rodan/proto430/firmware/i2c_read/list_helper.h

#ifndef __list_helper_h__
#define __list_helper_h__

struct list_struct {
    int val;
    struct list_struct *next;
};

struct list_struct *list_init(struct list_struct **head, struct list_struct **curr, const int val);
struct list_struct *list_add_node(struct list_struct **head, struct list_struct **curr, const int val);
struct list_struct *list_search(struct list_struct *head, int val, struct list_struct **prev);
int list_get_head(struct list_struct **head, int *val);
int list_rm_node(struct list_struct **head, struct list_struct **curr, const int val);
void list_print(struct list_struct *head);
int list_len(struct list_struct *head);
int list_free(struct list_struct **head);
int list_non_empty(struct list_struct *head);

#endif
